reg4liz/arduino_led_tester/img/2.jpg

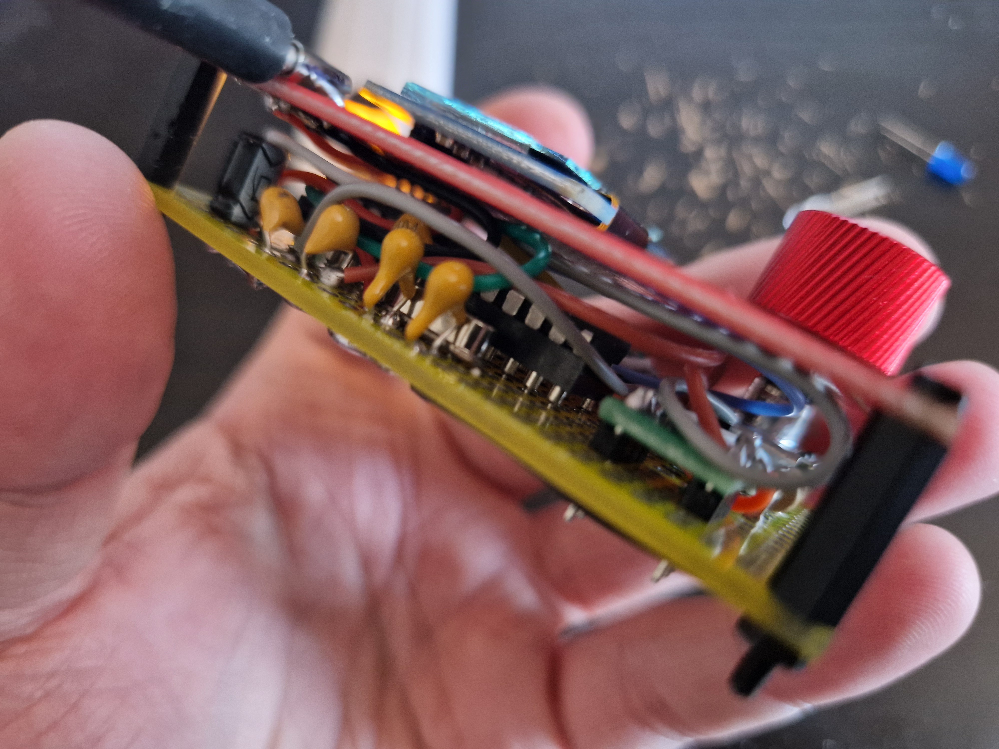
img/2.jpg
