reg4liz/arduino_led_tester/img/3.jpg

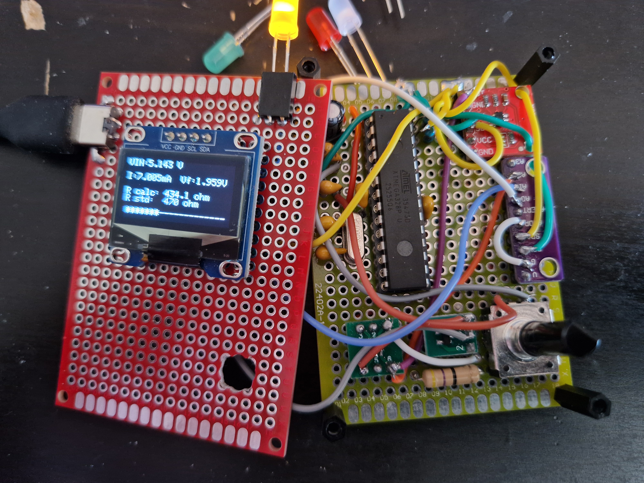
img/3.jpg
